petl/USB-midi-fader/pictures/v2/IMG_20220124_163709.jpg

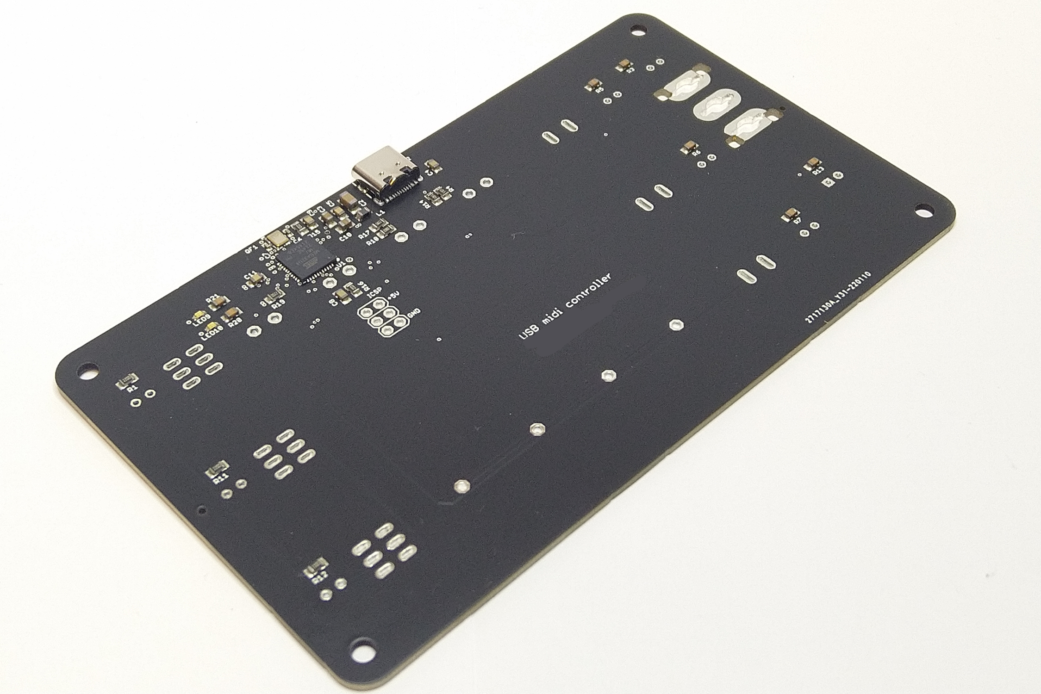
pictures/v2/IMG_20220124_163709.jpg
