petl/USB-midi-fader/pictures/v2/IMG_20220124_163744.jpg

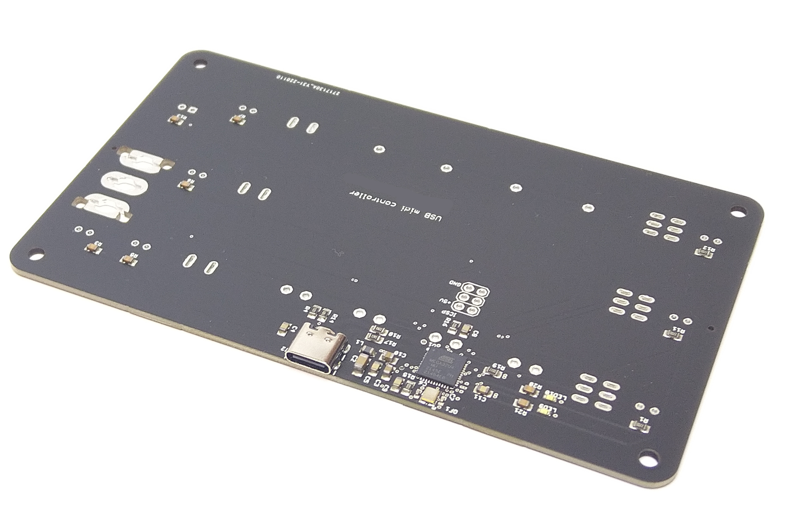
pictures/v2/IMG_20220124_163744.jpg
