petl/USB-midi-fader/pictures/v2/IMG_20220124_164212.jpg

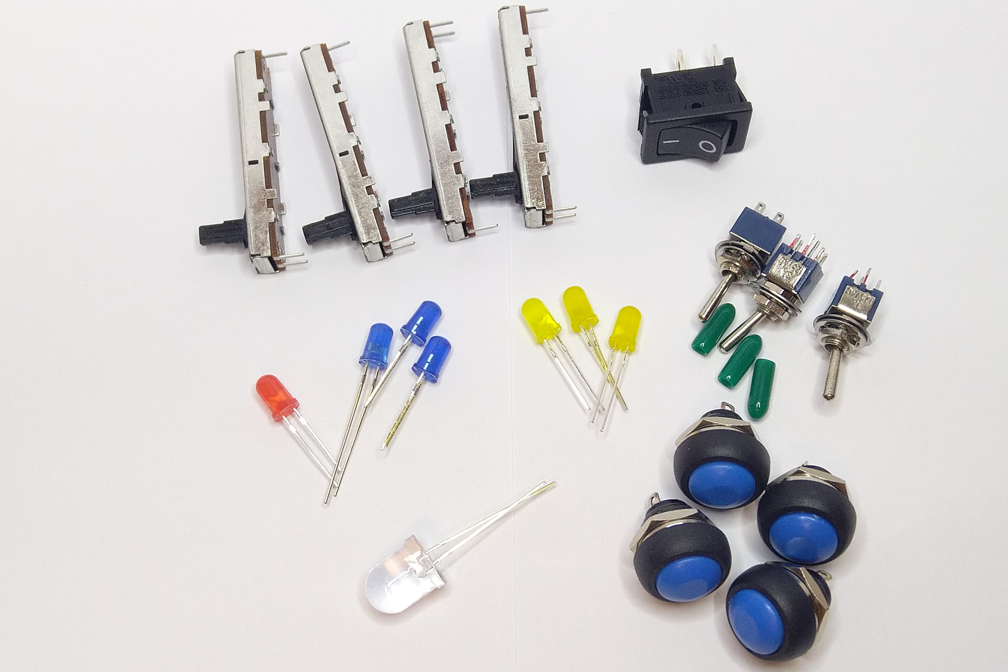
pictures/v2/IMG_20220124_164212.jpg
