petl/USB-midi-fader/pictures/v2/IMG_20220124_164330.jpg

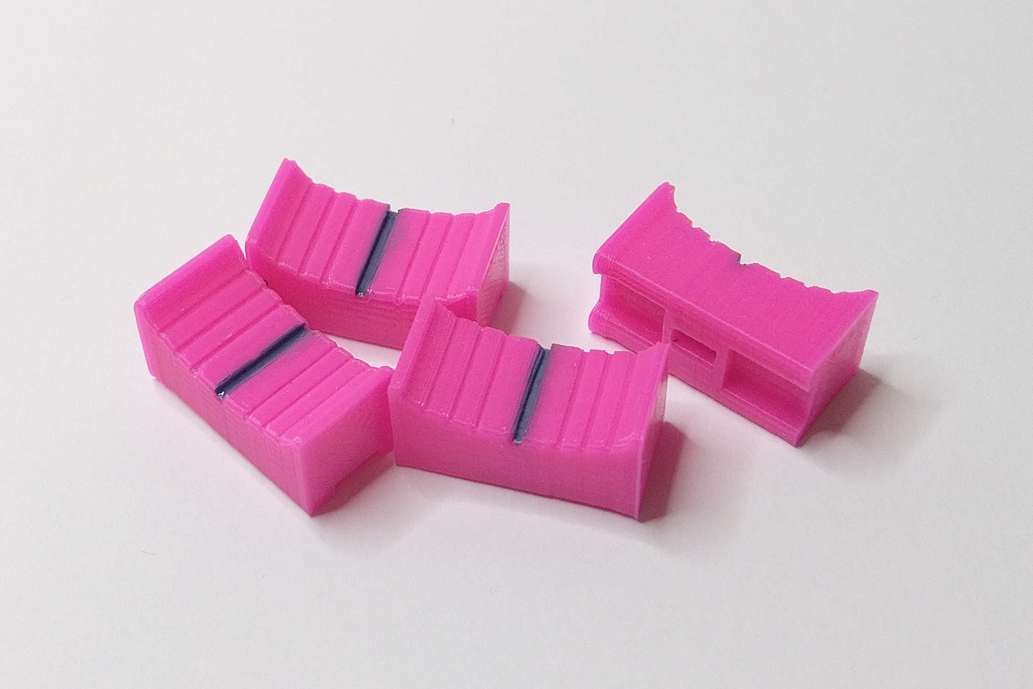
pictures/v2/IMG_20220124_164330.jpg
