petl/USB-midi-fader/pictures/v2/IMG_20220124_165818.jpg

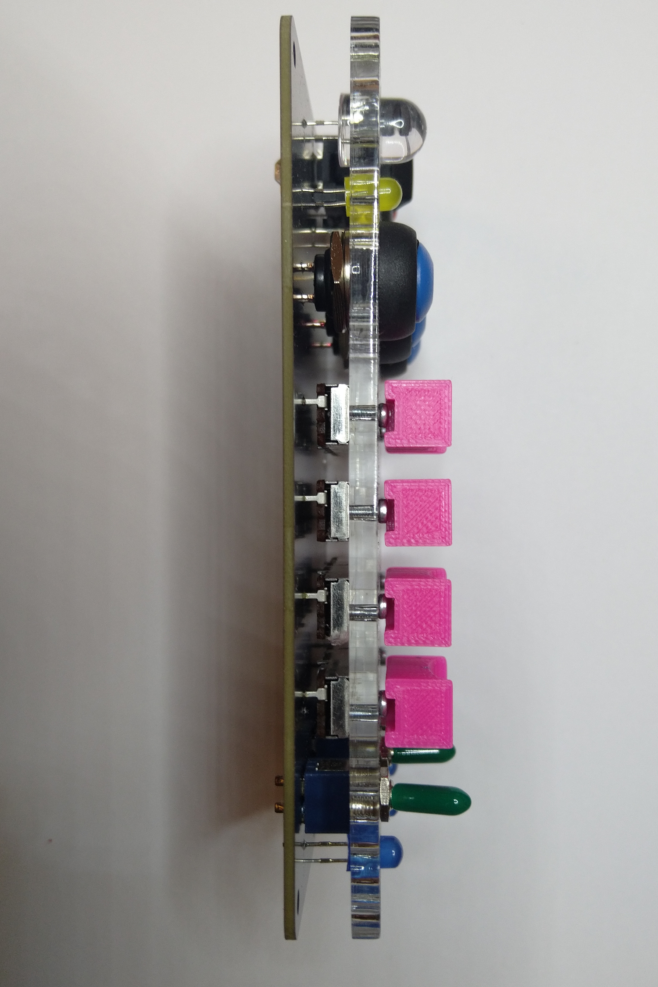
pictures/v2/IMG_20220124_165818.jpg
