petl/USB-midi-fader/pictures/v2/IMG_20220127_143834.jpg

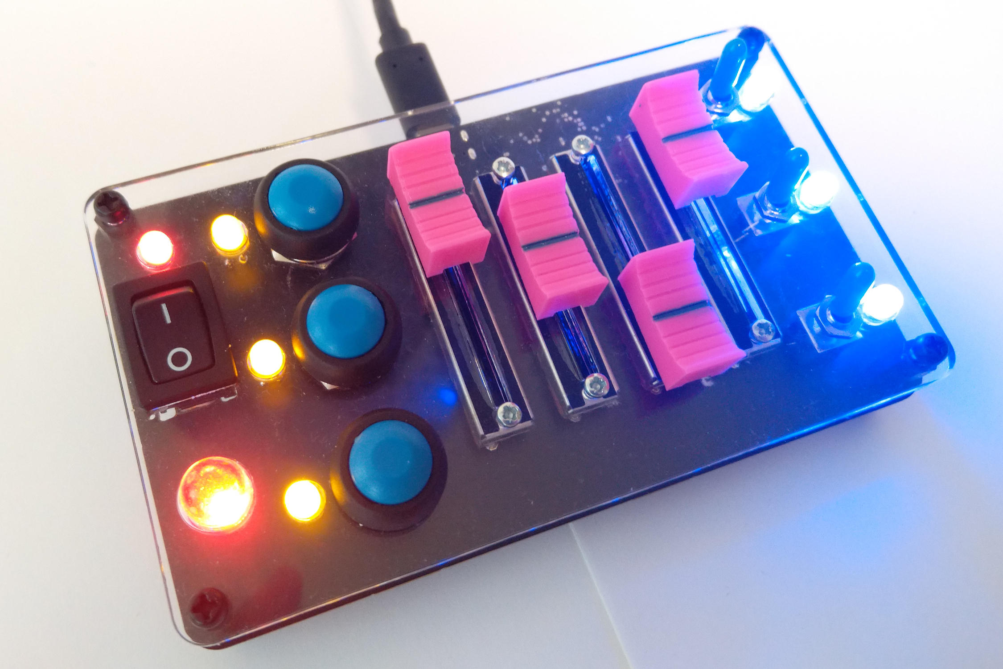
pictures/v2/IMG_20220127_143834.jpg
