petl/USB-midi-fader/pictures/v2/IMG_20220127_144213.jpg

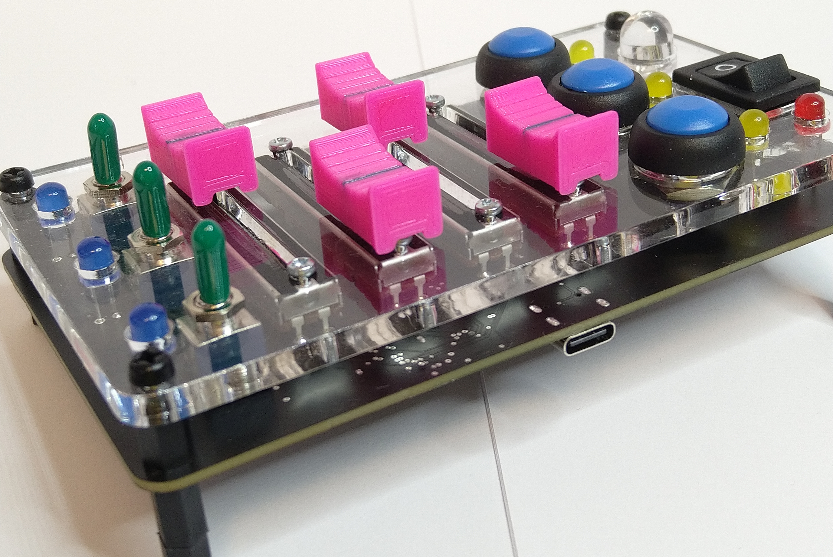
pictures/v2/IMG_20220127_144213.jpg
