petl/USB-midi-fader/pictures/v2/IMG_20220127_144238.jpg

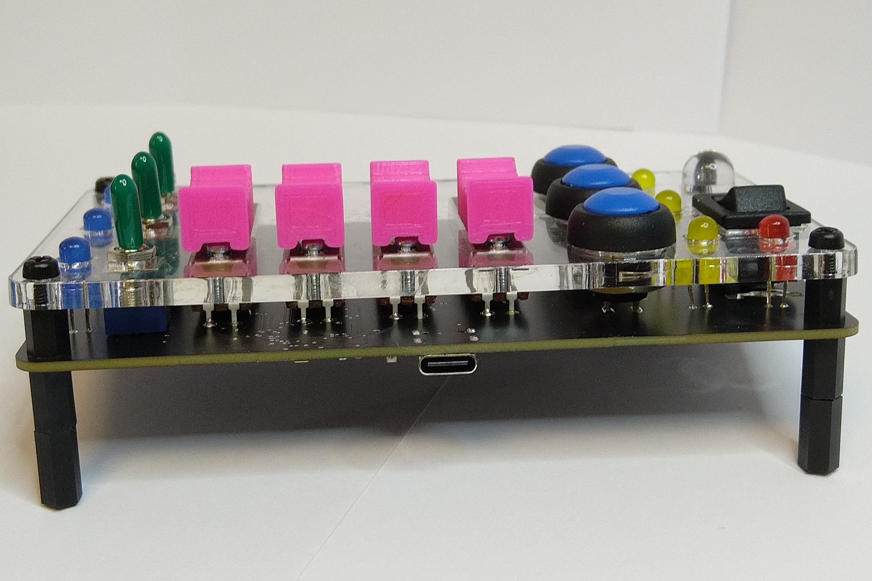
pictures/v2/IMG_20220127_144238.jpg
