petl/USB-midi-fader/pictures/v2/IMG_20220127_144242.jpg

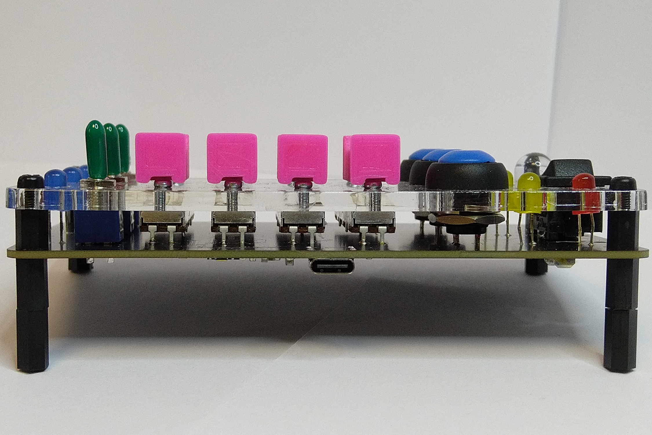
pictures/v2/IMG_20220127_144242.jpg
