petl/USB-midi-fader/pictures/v2/IMG_20220127_151032.jpg

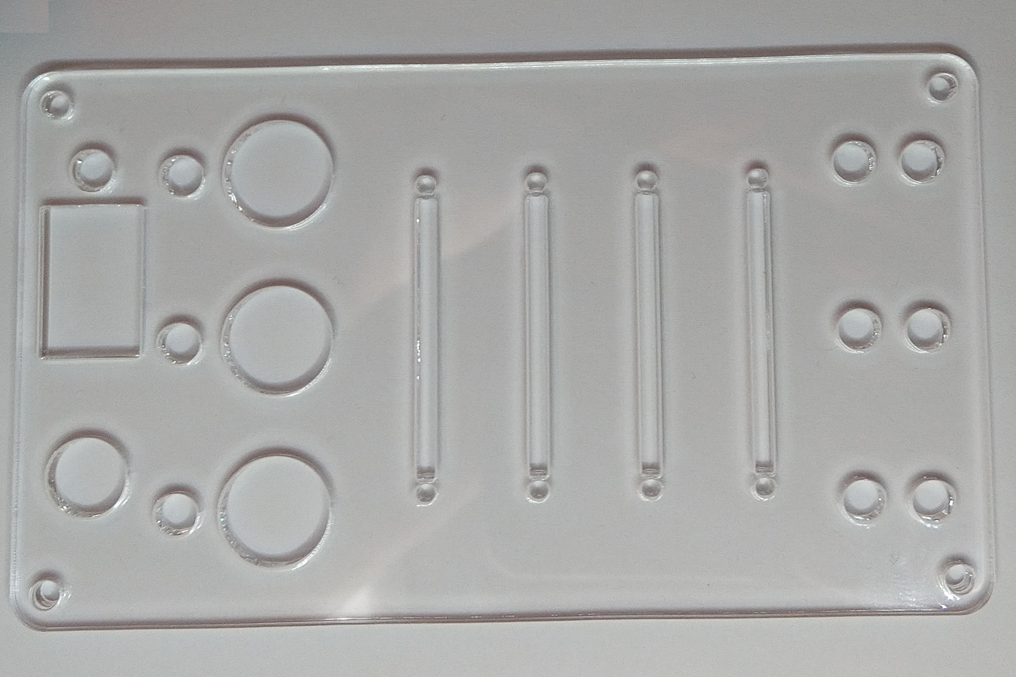
pictures/v2/IMG_20220127_151032.jpg
