petl/USB-midi-fader/pictures/v2/IMG_20220127_161556.jpg

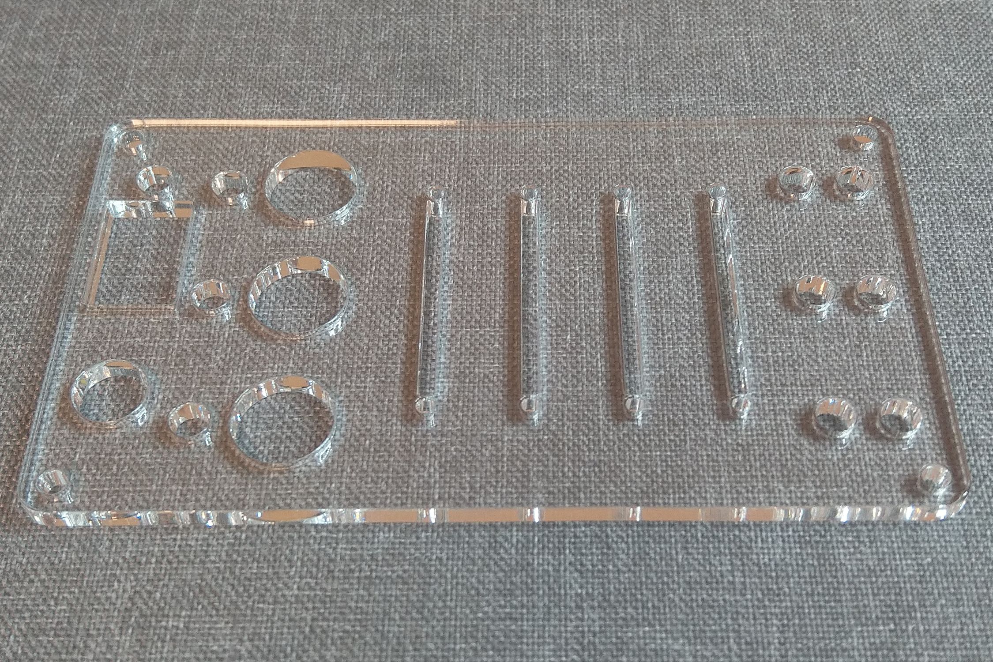
pictures/v2/IMG_20220127_161556.jpg
