petl/USB-midi-fader/schematics/USB_midi_controller.sch

## EAGLE design schematics/USB_midi_controller.sch (2021-12-29)

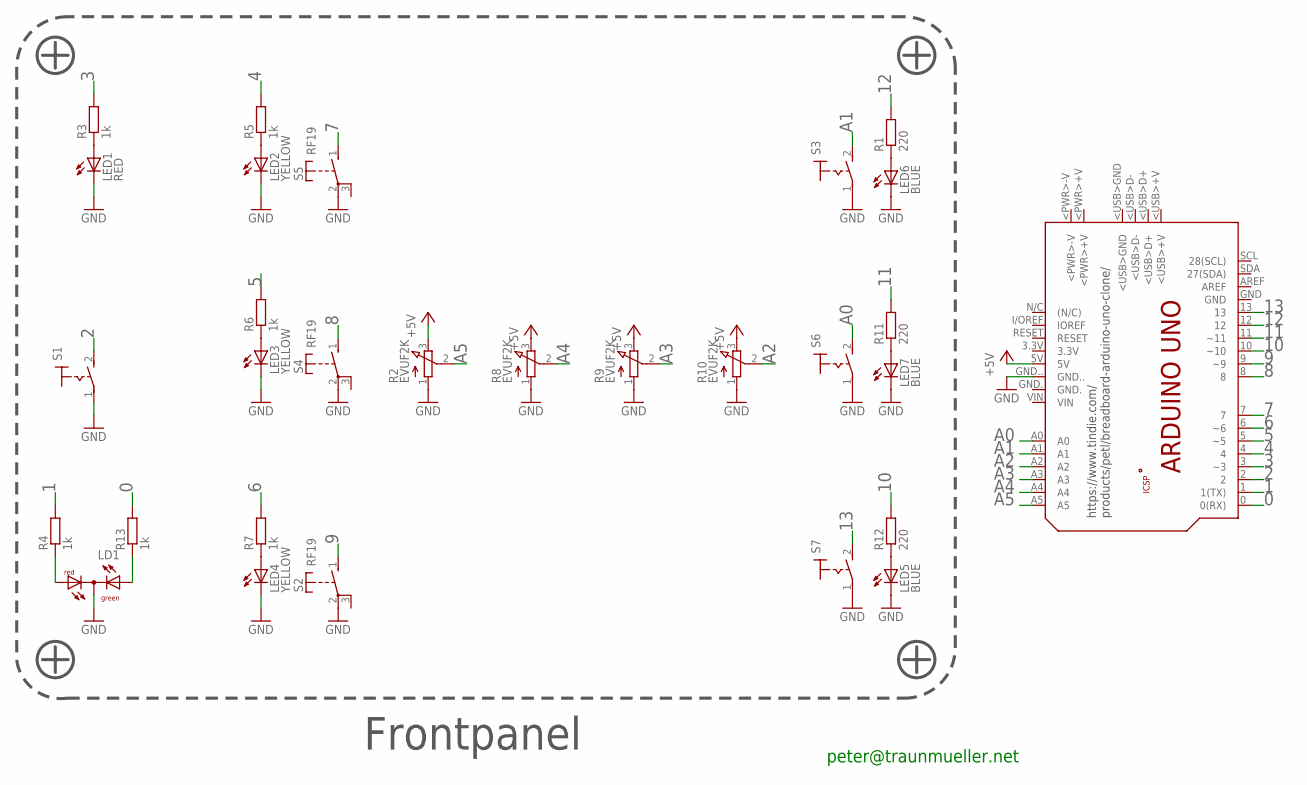
[picture p29: schematic USB_midi_controller.sch]

Parts:
LD1: DUOLED-RG-C; DUOLED-C-5MM
LED1: RED; LED5MM
LED2, LED3, LED4: YELLOW; LED5MM
LED5, LED6, LED7: BLUE; LED5MM
PCB1: ARDUINO_UNO
R1, R11, R12: 220; R0805
R2, R8, R9, R10: EVUF2K; EVUFXK
R3, R4, R5, R6, R7, R13: 1k; R0805
S1, S3, S6, S7: KSR224G
S2, S4, S5: RF19

Connections:
0: PCB1.0 (0(RX)), R13.2
1: PCB1.1 (1(TX)), R4.2
2: PCB1.2, S1.2 (S)
3: PCB1.3 (~3), R3.2
4: PCB1.4, R5.2
5: PCB1.5 (~5), R6.2
6: PCB1.6 (~6), R7.2
7: PCB1.7, S5.1 (S)
8: PCB1.8, S4.1 (S)
9: PCB1.9 (~9), S2.1 (S)
10: PCB1.10 (~10), R12.2
11: PCB1.11 (~11), R11.2
12: PCB1.12, R1.2
13: PCB1.13, S7.2 (S)
+5V: PCB1.5V, R2.3 (E), R8.3 (E), R9.3 (E), R10.3 (E)
A0: PCB1.A0, S6.2 (S)
A1: PCB1.A1, S3.2 (S)
A2: PCB1.A2, R10.2 (S)
A3: PCB1.A3, R9.2 (S)
A4: PCB1.A4, R8.2 (S)
A5: PCB1.A5, R2.2 (S)
GND: LD1.C, LED1.K (C), LED2.K (C), LED3.K (C), LED4.K (C), LED5.K (C), LED6.K (C), LED7.K (C), PCB1.GND.., R2.1 (A), R8.1 (A), R9.1 (A), R10.1 (A), S1.1, S2.2, S3.1, S4.2, S5.2, S6.1, S7.1
unnamed: LED1.A, R3.1
unnamed: LED2.A, R5.1
unnamed: LED3.A, R6.1
unnamed: LED4.A, R7.1
unnamed: LED6.A, R1.1
unnamed: LED7.A, R11.1
unnamed: LED5.A, R12.1
unnamed: LD1.AR, R4.1
unnamed: LD1.AX (AG), R13.1

Notes on the sheet:
peter@traunmueller.net
Frontpanel
https://www.tindie.com/ products/petl/breadboard-arduino-uno-clone/
